Fdepraetre/PinokioProject/img/5kg_load.JPG

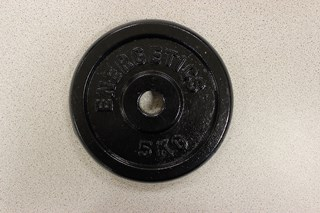
img/5kg_load.JPG
