Fdepraetre/PinokioProject/img/actuator_arm.JPG

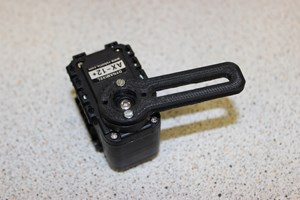
img/actuator_arm.JPG
