Fdepraetre/PinokioProject/img/arm.JPG

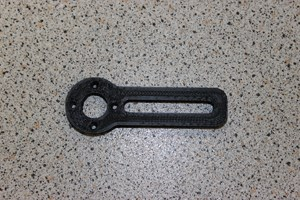
img/arm.JPG
