Fdepraetre/PinokioProject/img/baker_bowl.JPG

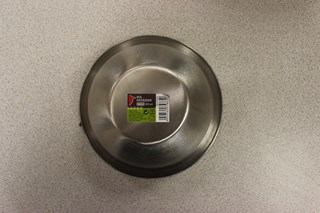
img/baker_bowl.JPG
