Fdepraetre/PinokioProject/img/base_part2_actuator_mounted_2.JPG

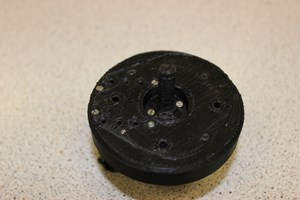
img/base_part2_actuator_mounted_2.JPG
