Fdepraetre/PinokioProject/img/common_anode_led.jpg

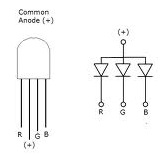
img/common_anode_led.jpg
