Fdepraetre/PinokioProject/img/finished_lamp.JPG

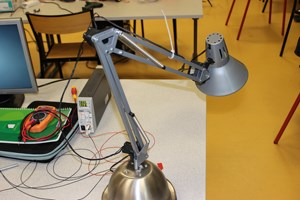
img/finished_lamp.JPG
