Fdepraetre/PinokioProject/img/finished_lamp_red.JPG

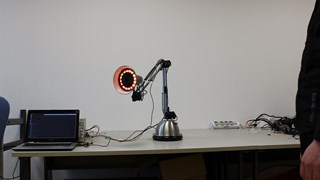
img/finished_lamp_red.JPG
