Fdepraetre/PinokioProject/img/finished_lamp_top_view.JPG

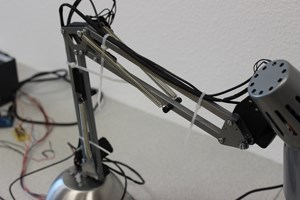
img/finished_lamp_top_view.JPG
