Fdepraetre/PinokioProject/img/head_actuator mounted.JPG

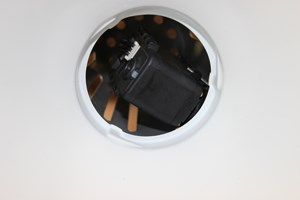
img/head_actuator mounted.JPG
