Fdepraetre/PinokioProject/img/head_actuator+joint3.JPG

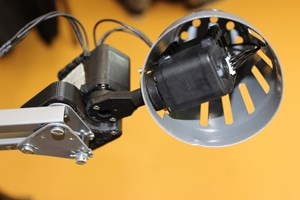
img/head_actuator+joint3.JPG
