Fdepraetre/PinokioProject/img/head_mounted2.JPG

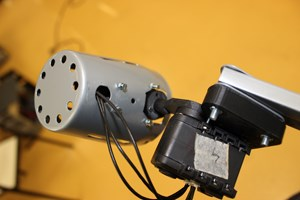
img/head_mounted2.JPG
