Fdepraetre/PinokioProject/img/joint1_mounted1.JPG

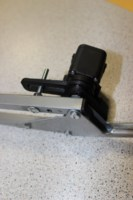
img/joint1_mounted1.JPG
