Fdepraetre/PinokioProject/img/joint1_mounted2.JPG

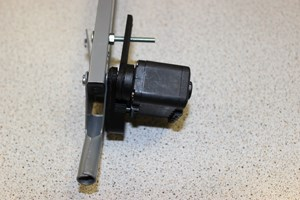
img/joint1_mounted2.JPG
