Fdepraetre/PinokioProject/img/joint1_mounted3.JPG

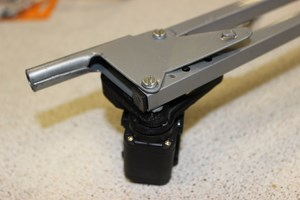
img/joint1_mounted3.JPG
