Fdepraetre/PinokioProject/img/joint1_mounted4.JPG

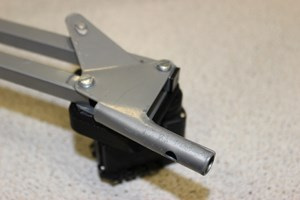
img/joint1_mounted4.JPG
