Fdepraetre/PinokioProject/img/joint2_mounted5.JPG

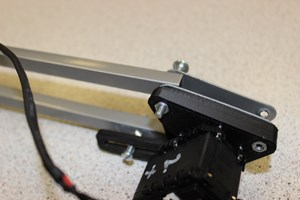
img/joint2_mounted5.JPG
