Fdepraetre/PinokioProject/img/joint2_mounted.JPG

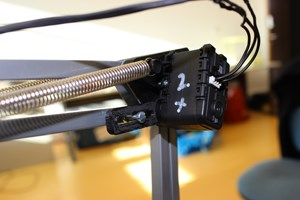
img/joint2_mounted.JPG
