Fdepraetre/PinokioProject/img/joint2_mounted_1.JPG

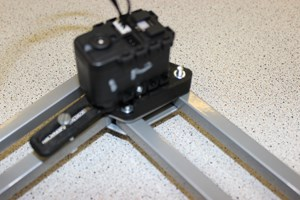
img/joint2_mounted_1.JPG
