Fdepraetre/PinokioProject/img/joint2_mounted_2.JPG

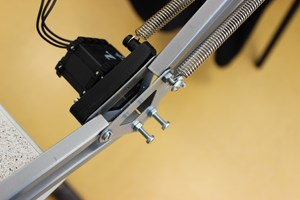
img/joint2_mounted_2.JPG
