Fdepraetre/PinokioProject/img/joint2_mounted_3.JPG

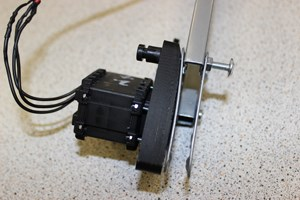
img/joint2_mounted_3.JPG
