Fdepraetre/PinokioProject/img/joint2_mounted_4.JPG

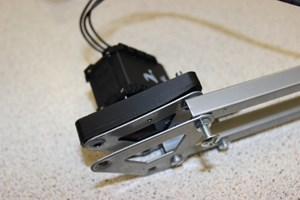
img/joint2_mounted_4.JPG
