Fdepraetre/PinokioProject/img/joint2_plastic_part.JPG

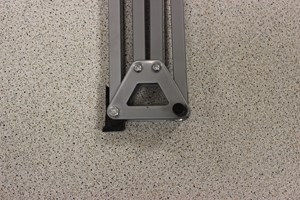
img/joint2_plastic_part.JPG
