Fdepraetre/PinokioProject/img/joint3.JPG

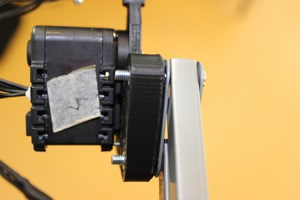
img/joint3.JPG
