Fdepraetre/PinokioProject/img/lamp_box.JPG

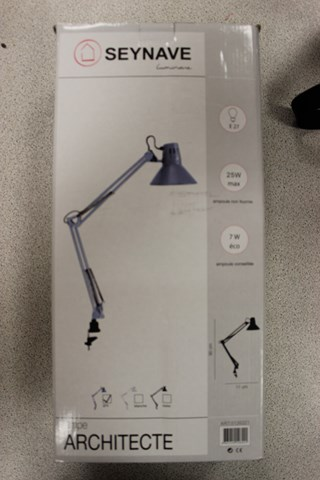
img/lamp_box.JPG
