Fdepraetre/PinokioProject/img/lamp_dissambled.JPG

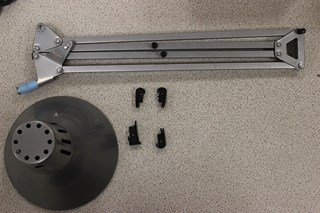
img/lamp_dissambled.JPG
