Fdepraetre/PinokioProject/img/lamp_finished_green.JPG

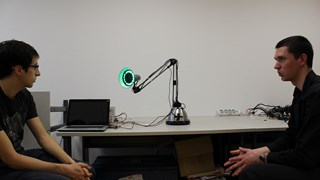
img/lamp_finished_green.JPG
