Fdepraetre/PinokioProject/img/lamp_finished_green_1.JPG

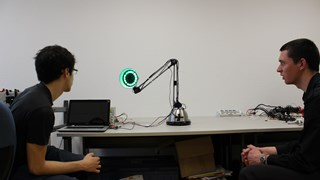
img/lamp_finished_green_1.JPG
