Fdepraetre/PinokioProject/img/lamp_led_unmounted.JPG

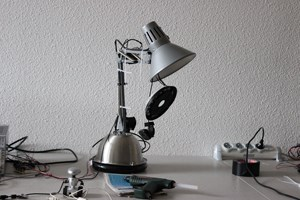
img/lamp_led_unmounted.JPG
