Fdepraetre/PinokioProject/img/lamp_top.JPG

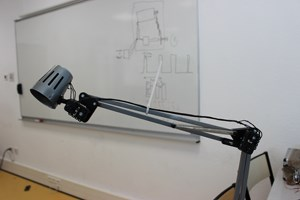
img/lamp_top.JPG
