Fdepraetre/PinokioProject/img/led_1.JPG

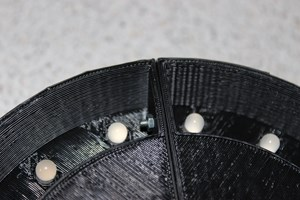
img/led_1.JPG
