Fdepraetre/PinokioProject/img/led_2.JPG

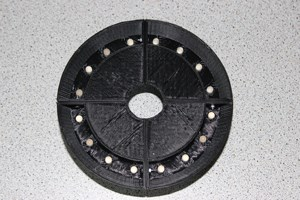
img/led_2.JPG
