Fdepraetre/PinokioProject/img/led_3.JPG

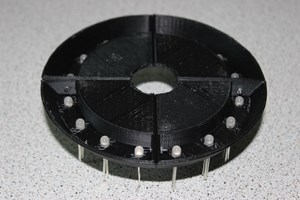
img/led_3.JPG
