Fdepraetre/PinokioProject/img/led_4.JPG

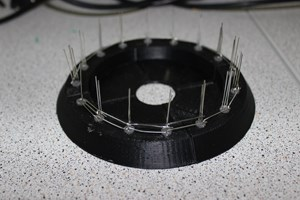
img/led_4.JPG
