Fdepraetre/PinokioProject/img/ledBoard.png

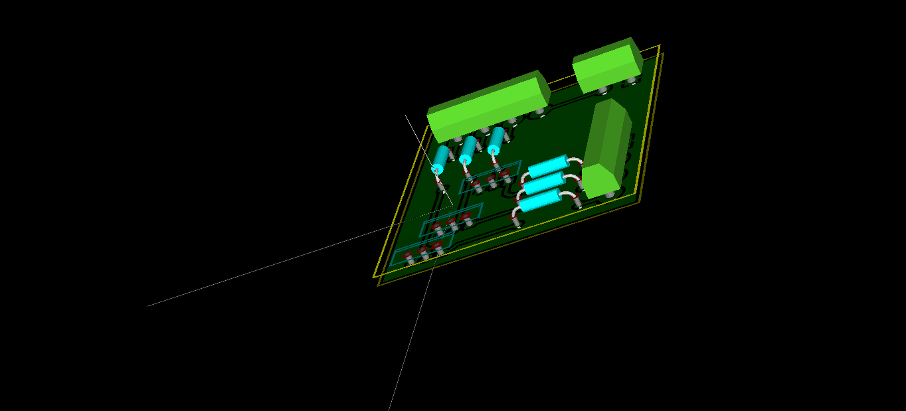
img/ledBoard.png
