Fdepraetre/PinokioProject/img/LedControlSchematic.png

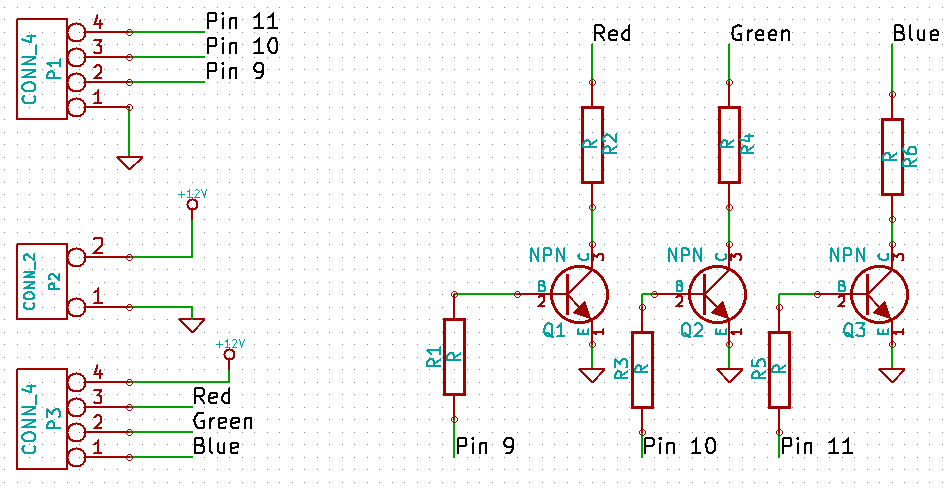
img/LedControlSchematic.png
