Fdepraetre/PinokioProject/img/part_ax12tobase.bmp

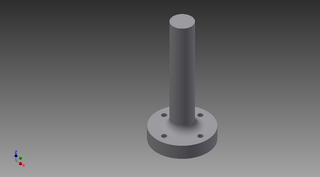
img/part_ax12tobase.bmp
