Fdepraetre/PinokioProject/img/part_bloc.bmp

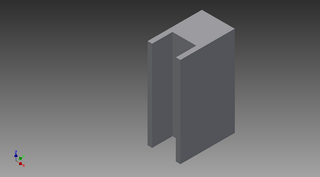
img/part_bloc.bmp
