Fdepraetre/PinokioProject/img/part_bottom_mx28_v1.bmp

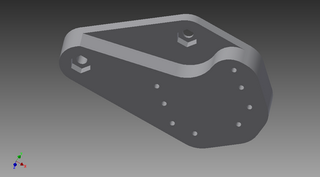
img/part_bottom_mx28_v1.bmp
