Fdepraetre/PinokioProject/img/part_bowl_ax12_support.bmp

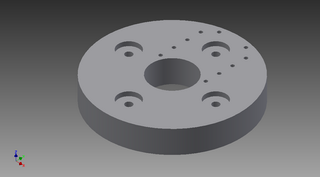
img/part_bowl_ax12_support.bmp
