Fdepraetre/PinokioProject/img/part_bowl_v1.bmp

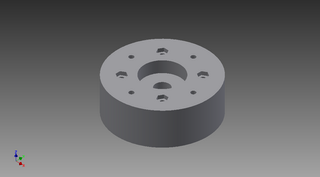
img/part_bowl_v1.bmp
