Fdepraetre/PinokioProject/img/part_head_inside.bmp

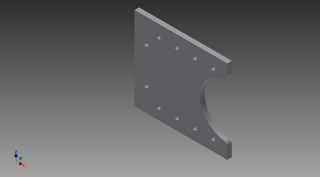
img/part_head_inside.bmp
