Fdepraetre/PinokioProject/img/part_led_circle.bmp

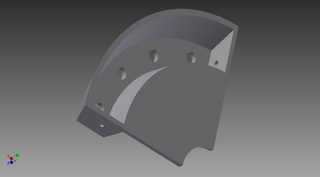
img/part_led_circle.bmp
