Fdepraetre/PinokioProject/img/part_middle_v1.bmp

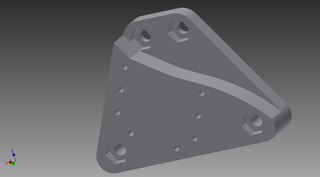
img/part_middle_v1.bmp
