Fdepraetre/PinokioProject/img/part_neck_v2.1.bmp

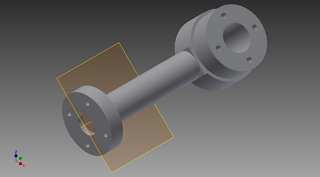
img/part_neck_v2.1.bmp
