Fdepraetre/PinokioProject/img/part_top_v4.bmp

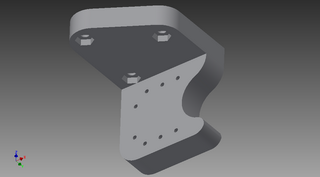
img/part_top_v4.bmp
