Fdepraetre/PinokioProject/img/square_tube_cut.JPG

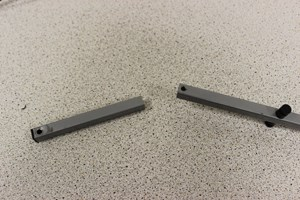
img/square_tube_cut.JPG
