Fdepraetre/PinokioProject/img/square_tube_hole.JPG

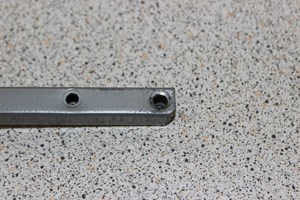
img/square_tube_hole.JPG
