Fdepraetre/PinokioProject/img/stem1.JPG

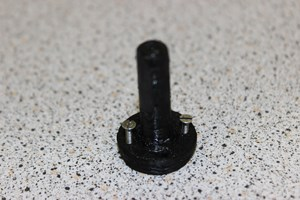
img/stem1.JPG
