Fdepraetre/PinokioProject/img/stem2.JPG

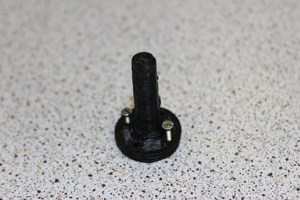
img/stem2.JPG
