Fdepraetre/PinokioProject/img/tube_drilled1.JPG

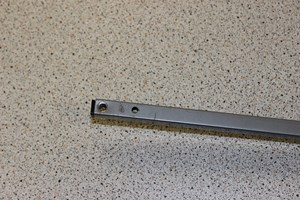
img/tube_drilled1.JPG
