Fdepraetre/PinokioProject/img/tube_drilled2.JPG

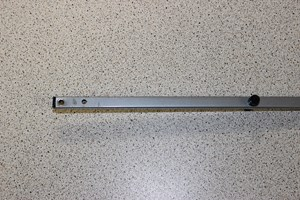
img/tube_drilled2.JPG
