Fdepraetre/PinokioProject/img/usb2dynamixel.JPG

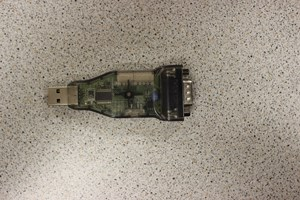
img/usb2dynamixel.JPG
