Fdepraetre/PinokioProject/parts/head_inside.stl

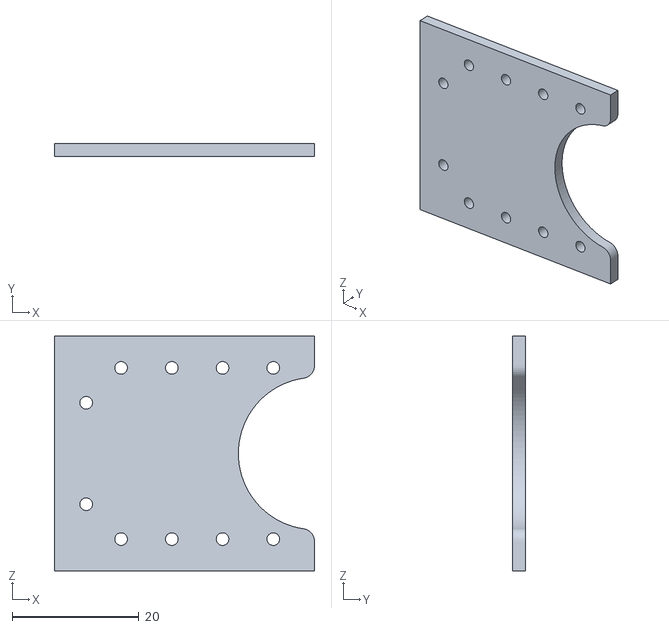
[picture p73: CAD file, 2014-01-16]
parts/head_inside.stl
41.0 x 2.00 x 37.0
