Fdepraetre/PinokioProject/parts/middle_v1.stl

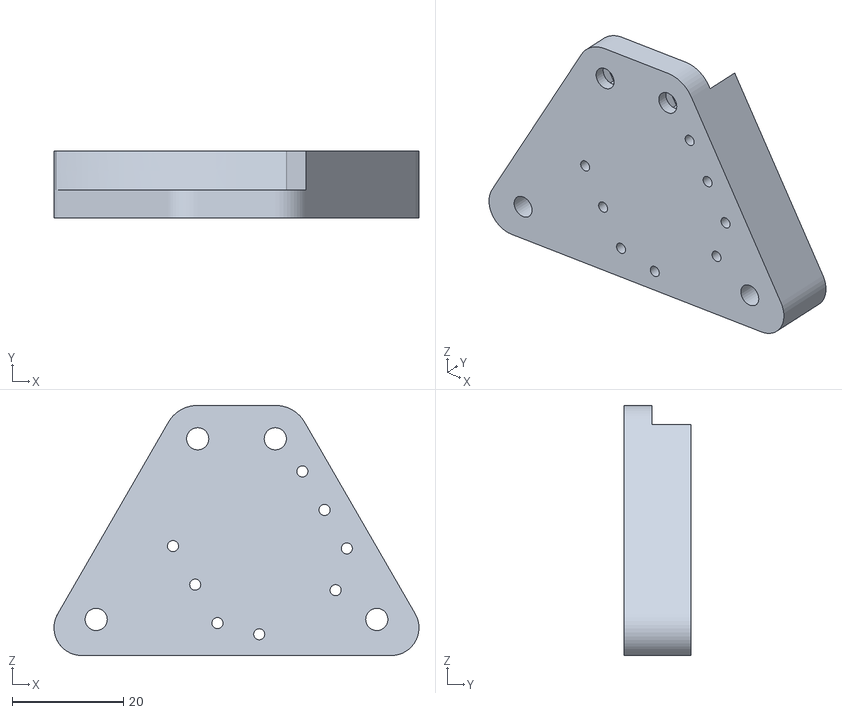
[picture p74: CAD file, 2014-01-14]
parts/middle_v1.stl
65.7 x 12.0 x 45.0
