Fdepraetre/PinokioProject/parts/oldparts/bowl_v1.stl

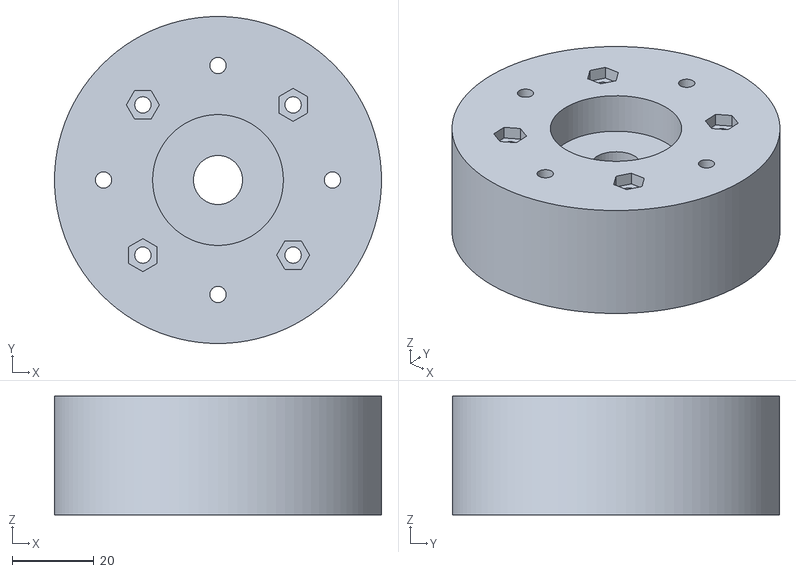
[picture p75: CAD file, 2014-01-16]
parts/oldparts/bowl_v1.stl
80.0 x 80.0 x 29.0
