Fdepraetre/PinokioProject/parts/top_circle.stl

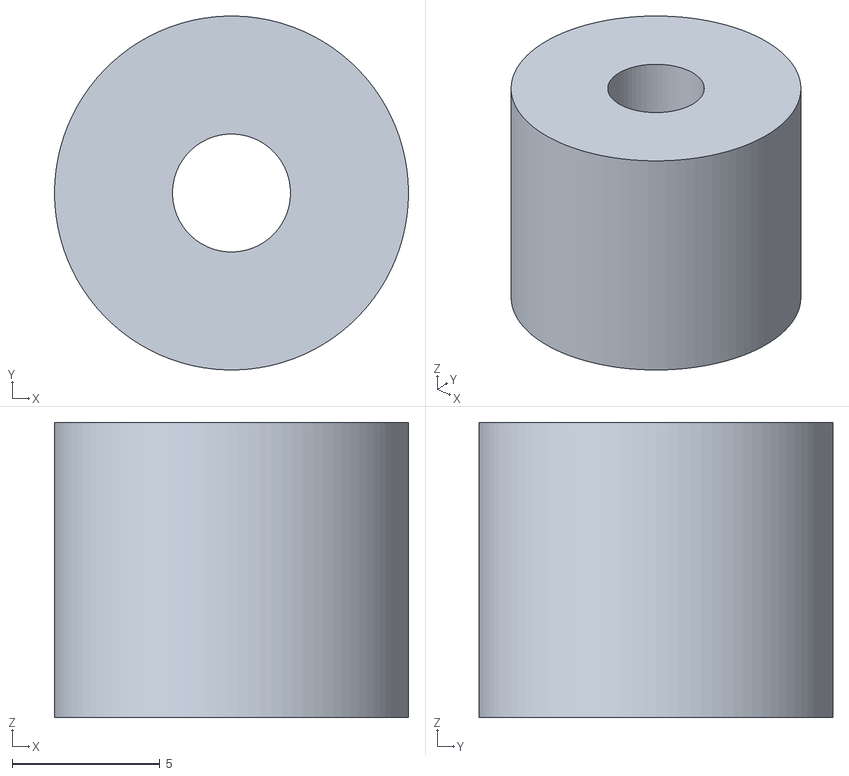
[picture p76: CAD file, 2014-01-14]
parts/top_circle.stl
12.0 x 12.0 x 10.0
