Fdepraetre/PinokioProject/parts/moving_arm.stl

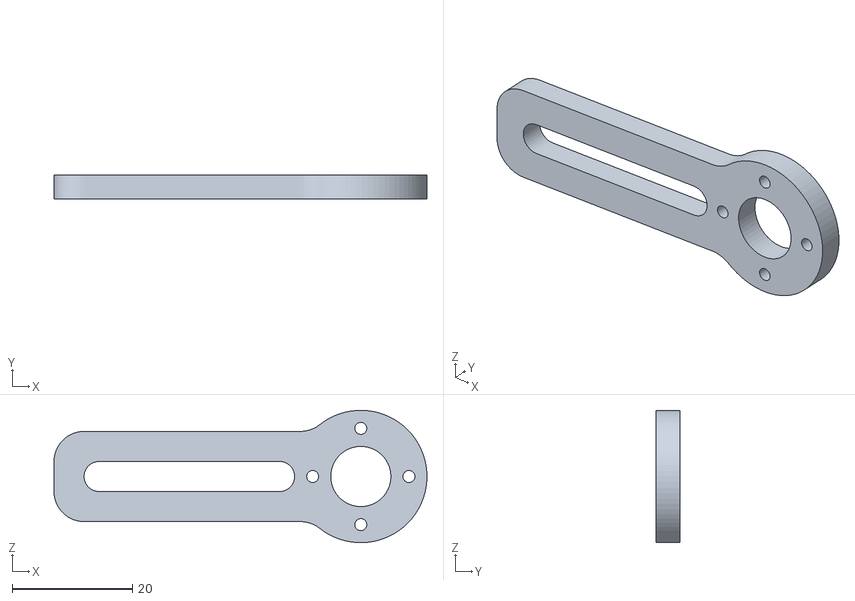
[picture p77: CAD file, 2014-01-14]
parts/moving_arm.stl
62.0 x 4.00 x 22.0
