Fdepraetre/PinokioProject/img/base_step2.JPG

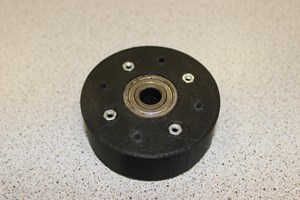
img/base_step2.JPG
