Fdepraetre/PinokioProject/img/base_step3.JPG

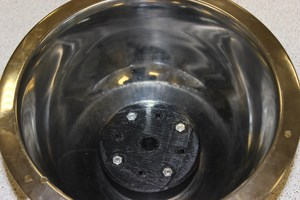
img/base_step3.JPG
