Fdepraetre/PinokioProject/img/base_step4.JPG

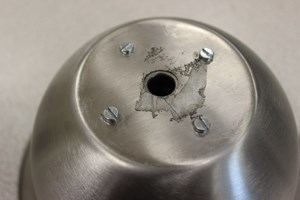
img/base_step4.JPG
