Fdepraetre/PinokioProject/img/base_step5.JPG

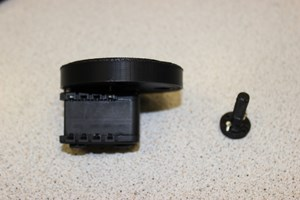
img/base_step5.JPG
