Fdepraetre/PinokioProject/img/base_step7.JPG

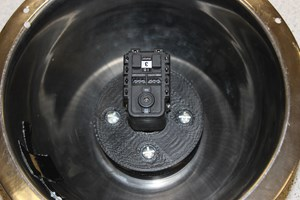
img/base_step7.JPG
