Fdepraetre/PinokioProject/img/base_step8.JPG

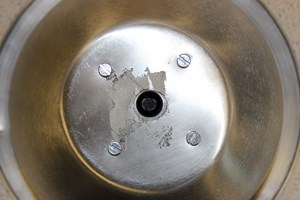
img/base_step8.JPG
