Fdepraetre/PinokioProject/img/bowl_step3.JPG

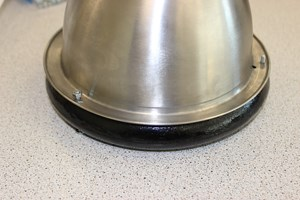
img/bowl_step3.JPG
