Fdepraetre/PinokioProject/img/bowl_step4.JPG

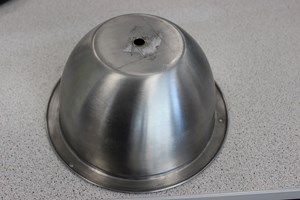
img/bowl_step4.JPG
