Fdepraetre/PinokioProject/img/bowl_step5.JPG

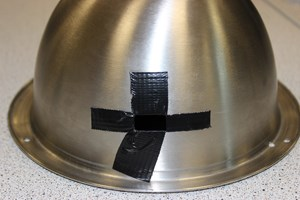
img/bowl_step5.JPG
