Fdepraetre/PinokioProject/img/head_step1-2.JPG

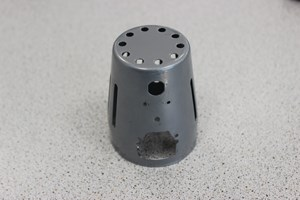
img/head_step1-2.JPG
