Fdepraetre/PinokioProject/img/head_step1.JPG

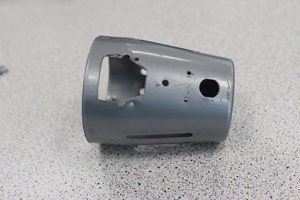
img/head_step1.JPG
