Fdepraetre/PinokioProject/img/head_step2-2.JPG

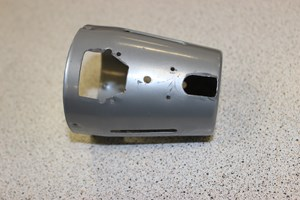
img/head_step2-2.JPG
