Fdepraetre/PinokioProject/img/head_step2.JPG

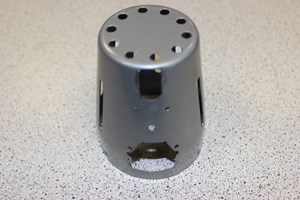
img/head_step2.JPG
