Fdepraetre/PinokioProject/img/head_step3-2.JPG

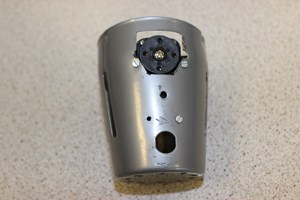
img/head_step3-2.JPG
