Fdepraetre/PinokioProject/img/head_step3.JPG

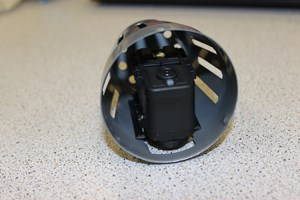
img/head_step3.JPG
