Fdepraetre/PinokioProject/img/head_step4.JPG

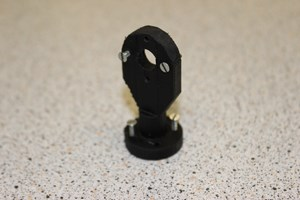
img/head_step4.JPG
