Fdepraetre/PinokioProject/img/head_step5.JPG

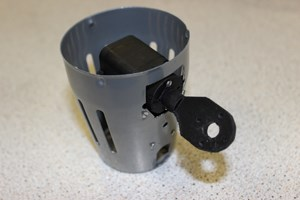
img/head_step5.JPG
