Fdepraetre/PinokioProject/img/joint1_step0.JPG

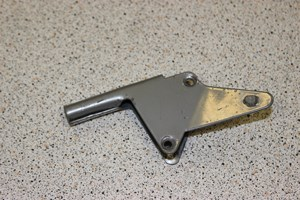
img/joint1_step0.JPG
