Fdepraetre/PinokioProject/img/joint1_step1.JPG

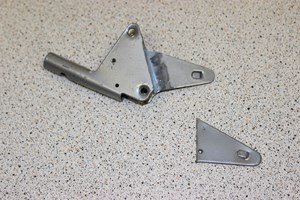
img/joint1_step1.JPG
