Fdepraetre/PinokioProject/img/joint1_step2.JPG

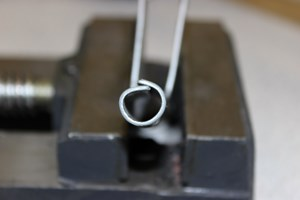
img/joint1_step2.JPG
