Fdepraetre/PinokioProject/img/joint1_step3.JPG

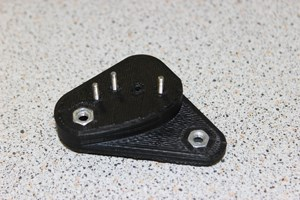
img/joint1_step3.JPG
