Fdepraetre/PinokioProject/img/joint2_step1.JPG

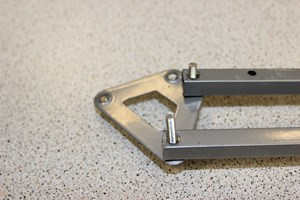
img/joint2_step1.JPG
