Fdepraetre/PinokioProject/img/joint2_step2.JPG

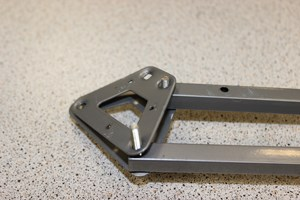
img/joint2_step2.JPG
