Fdepraetre/PinokioProject/img/joint2_step3.JPG

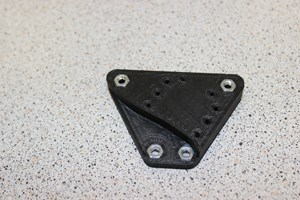
img/joint2_step3.JPG
