Fdepraetre/PinokioProject/img/joint2_step4.JPG

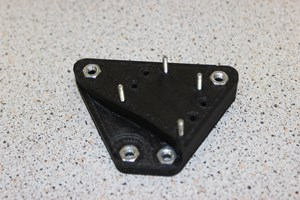
img/joint2_step4.JPG
