Fdepraetre/PinokioProject/img/joint2_step5.JPG

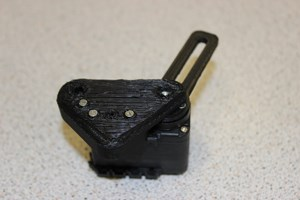
img/joint2_step5.JPG
