Fdepraetre/PinokioProject/img/joint2_step6.JPG

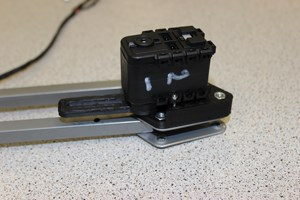
img/joint2_step6.JPG
