Fdepraetre/PinokioProject/img/joint2_step8.JPG

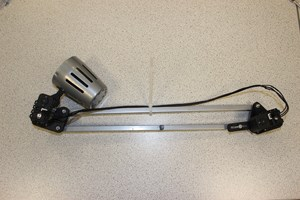
img/joint2_step8.JPG
