Fdepraetre/PinokioProject/img/joint3_step1.JPG

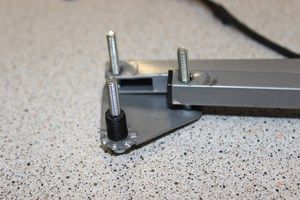
img/joint3_step1.JPG
