Fdepraetre/PinokioProject/img/joint3_step2.JPG

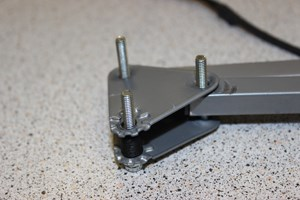
img/joint3_step2.JPG
