Fdepraetre/PinokioProject/img/joint3_step3.JPG

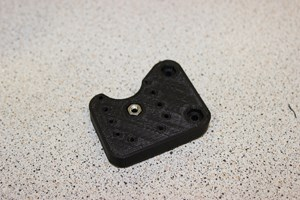
img/joint3_step3.JPG
