Fdepraetre/PinokioProject/img/joint3_step4.JPG

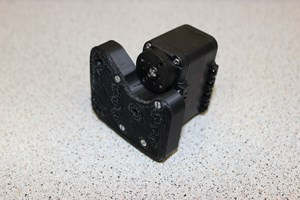
img/joint3_step4.JPG
