Fdepraetre/PinokioProject/img/joint3_step5-2.JPG

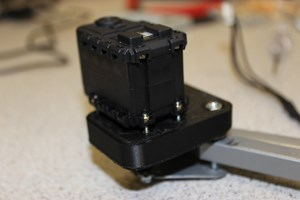
img/joint3_step5-2.JPG
