Fdepraetre/PinokioProject/img/joint3_step5.JPG

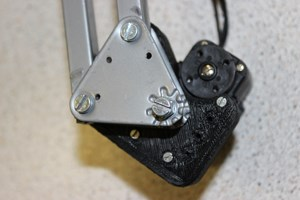
img/joint3_step5.JPG
