Fdepraetre/PinokioProject/img/joint3_step6.JPG

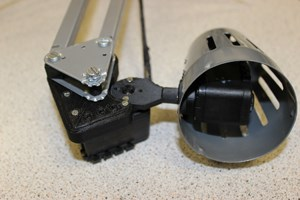
img/joint3_step6.JPG
