Fdepraetre/PinokioProject/img/led_step0.JPG

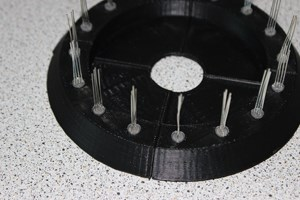
img/led_step0.JPG
