Fdepraetre/PinokioProject/img/led_step1.JPG

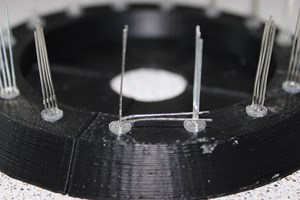
img/led_step1.JPG
