Fdepraetre/PinokioProject/img/led_step3.JPG

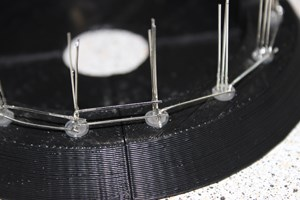
img/led_step3.JPG
