Fdepraetre/PinokioProject/img/led_step4.JPG

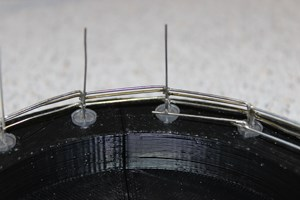
img/led_step4.JPG
