Fdepraetre/PinokioProject/img/led_step5.JPG

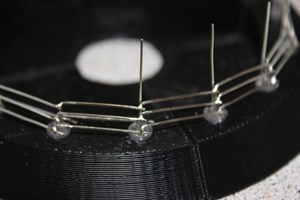
img/led_step5.JPG
