Fdepraetre/PinokioProject/img/led_step6.JPG

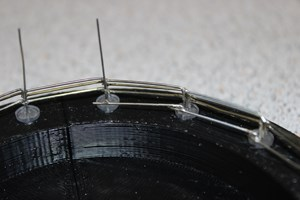
img/led_step6.JPG
