Fdepraetre/PinokioProject/img/led_step7.JPG

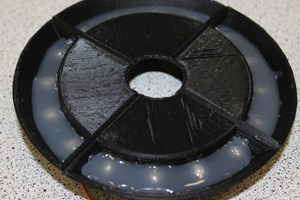
img/led_step7.JPG
