Fdepraetre/PinokioProject/img/led_step8.JPG

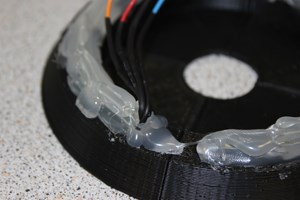
img/led_step8.JPG
