Fdepraetre/PinokioProject/img/led_step9.JPG

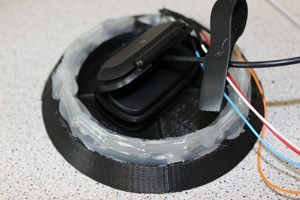
img/led_step9.JPG
