Fdepraetre/PinokioProject/img/led_step10.JPG

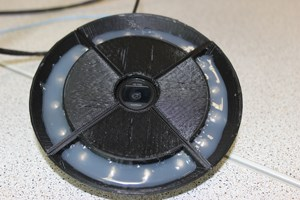
img/led_step10.JPG
