Fdepraetre/PinokioProject/img/load_step1.JPG

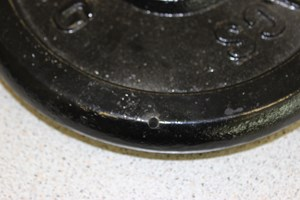
img/load_step1.JPG
