Fdepraetre/PinokioProject/img/load_step2.JPG

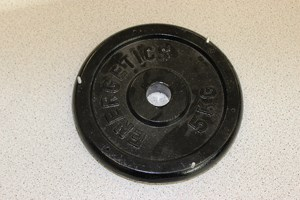
img/load_step2.JPG
