Fdepraetre/PinokioProject/elec/led.sch

## KiCad design elec/led.sch (2014-01-29)

Schematic: led.sch

Parts:
P1, P3: CONN_4
P2: CONN_2
Q1, Q2, Q3: NPN
R1, R2, R3, R4, R5, R6: R
