Fdepraetre/PinokioProject/src/userInterface/gui.py

import sys
import wx
import time
import threading
sys.path.insert(0, "../settings/")
import settings
sys.path.insert(0, "../control/")
import motorControl
sys.path.insert(0, "../traj/")
import trajectoryController
sys.path.insert(0, "../arduino/")
import python2arduino

class MyFrame(wx.Frame):
    def __init__(self, parent, id, title):
        wx.Frame.__init__(self, parent, id, title, wx.DefaultPosition, (800, 600))

        hbox= wx.BoxSizer(wx.HORIZONTAL)
        vbox = wx.BoxSizer(wx.VERTICAL)
        hboxcontrols = wx.BoxSizer(wx.HORIZONTAL)
        hboxlist = wx.BoxSizer(wx.HORIZONTAL)

        vbox.Add(hboxcontrols, 1, wx.EXPAND)
        vbox.Add(hboxlist, 1, wx.EXPAND)

        #comment load motor and load led when working on gui
        #load motor
        motorSettings = settings.MotorSettings().get()
        self.motorController = motorControl.MotorControl(motorSettings)
        self.motorController.setAllSpeed(100)
        #parse motor setting to get min and max angle, store result in hash motors
        motors = {}
        motorsConfig=motorSettings["motorConfig"]
        for motor in motorsConfig:
            motors[motor[3]] = [motor[1], motor[2]]

        #load led
        self.ledController = python2arduino.Arduino()

        #uncomment when working on gui
        #motors = {"bowl": [0, 150], "bottom": [0, 150], "mid": [0, 150], "top": [0, 150], "head": [0, 150]}

        #visual element
  
        #bowl button
        pnlBowl = wx.Panel(self, -1, style=wx.SIMPLE_BORDER)
        hboxcontrols.Add(pnlBowl, 1, wx.ALL |wx.EXPAND, 1)
        self.sldBowl = wx.Slider(pnlBowl, -1, motors["bowl"][0], motors["bowl"][0], motors["bowl"][1], wx.DefaultPosition, (-1, -1), wx.SL_VERTICAL | wx.SL_LABELS)
        textBowl = wx.StaticText(pnlBowl, -1, 'Bowl')
        vboxBowl = wx.BoxSizer(wx.VERTICAL)
        vboxBowl.Add(self.sldBowl, 1, wx.CENTER, 0)
        vboxBowl.Add(textBowl, 1, wx.CENTER)
        pnlBowl.SetSizer(vboxBowl)

        #bottom button
        pnlBottom = wx.Panel(self, -1, style=wx.SIMPLE_BORDER)
        hboxcontrols.Add(pnlBottom, 1, wx.ALL | wx.EXPAND, 1)
        self.sldBottom = wx.Slider(pnlBottom, -1, motors["bottom"][1], motors["bottom"][0], motors["bottom"][1], wx.DefaultPosition, (-1, -1), wx.SL_VERTICAL | wx.SL_LABELS)
        textBottom = wx.StaticText(pnlBottom, -1, 'Bottom')
        vboxBottom = wx.BoxSizer(wx.VERTICAL)
        vboxBottom.Add(self.sldBottom, 1, wx.CENTER)
        vboxBottom.Add(textBottom, 1, wx.CENTER)
        pnlBottom.SetSizer(vboxBottom)

        #middle button
        pnlMiddle = wx.Panel(self, -1, style=wx.SIMPLE_BORDER)
        hboxcontrols.Add(pnlMiddle, 1, wx.ALL | wx.EXPAND, 1)
        self.sldMiddle = wx.Slider(pnlMiddle, -1, motors["mid"][0], motors["mid"][0], motors["mid"][1], wx.DefaultPosition, (-1, -1), wx.SL_VERTICAL | wx.SL_LABELS)
        textMiddle = wx.StaticText(pnlMiddle, -1, 'Middle')
        vboxMiddle= wx.BoxSizer(wx.VERTICAL)
        vboxMiddle.Add(self.sldMiddle, 1, wx.CENTER)
        vboxMiddle.Add(textMiddle, 1, wx.CENTER)
        pnlMiddle.SetSizer(vboxMiddle)

        #top button
        pnlTop = wx.Panel(self, -1, style=wx.SIMPLE_BORDER)
        hboxcontrols.Add(pnlTop, 1, wx.ALL | wx.EXPAND, 1)
        self.sldTop = wx.Slider(pnlTop, -1, motors["top"][0], motors["top"][0], motors["top"][1], wx.DefaultPosition, (-1, -1), wx.SL_VERTICAL | wx.SL_LABELS)
        textTop = wx.StaticText(pnlTop, -1, 'Top')
        vboxTop = wx.BoxSizer(wx.VERTICAL)
        vboxTop.Add(self.sldTop, 1, wx.CENTER)
        vboxTop.Add(textTop, 1, wx.CENTER)
        pnlTop.SetSizer(vboxTop)

        #head button
        pnlHead = wx.Panel(self, -1, style=wx.SIMPLE_BORDER)
        hboxcontrols.Add(pnlHead, 1, wx.ALL | wx.EXPAND, 1)
        self.sldHead = wx.Slider(pnlHead, -1, motors["head"][0], motors["head"][0], motors["head"][1], wx.DefaultPosition, (-1, -1), wx.SL_VERTICAL | wx.SL_LABELS)
        textHead = wx.StaticText(pnlHead, -1, 'Head')
        vboxHead = wx.BoxSizer(wx.VERTICAL)
        vboxHead.Add(self.sldHead, 1, wx.CENTER)
        vboxHead.Add(textHead, 1, wx.CENTER)
        pnlHead.SetSizer(vboxHead)

        #red button
        pnlRed = wx.Panel(self, -1, style=wx.SIMPLE_BORDER)
        hboxcontrols.Add(pnlRed, 1, wx.ALL | wx.EXPAND, 1)
        self.sldRed = wx.Slider(pnlRed, -1, 0, 0, 255, wx.DefaultPosition, (-1, -1), wx.SL_VERTICAL | wx.SL_LABELS)
        textRed = wx.StaticText(pnlRed, -1, 'Red')
        vboxRed = wx.BoxSizer(wx.VERTICAL)
        vboxRed.Add(self.sldRed, 1, wx.CENTER)
        vboxRed.Add(textRed, 1, wx.CENTER)
        pnlRed.SetSizer(vboxRed)

        #green button
        pnlGreen = wx.Panel(self, -1, style=wx.SIMPLE_BORDER)
        hboxcontrols.Add(pnlGreen, 1, wx.ALL | wx.EXPAND, 1)
        self.sldGreen = wx.Slider(pnlGreen, -1, 0, 0, 255, wx.DefaultPosition, (-1, -1), wx.SL_VERTICAL | wx.SL_LABELS)
        textGreen = wx.StaticText(pnlGreen, -1, 'Green')
        vboxGreen = wx.BoxSizer(wx.VERTICAL)
        vboxGreen.Add(self.sldGreen, 1, wx.CENTER)
        vboxGreen.Add(textGreen, 1, wx.CENTER)
        pnlGreen.SetSizer(vboxGreen)

        #blue button
        pnlBlue = wx.Panel(self, -1, style=wx.SIMPLE_BORDER)
        hboxcontrols.Add(pnlBlue, 1, wx.ALL | wx.EXPAND, 1)
        self.sldBlue = wx.Slider(pnlBlue, -1, 0, 0, 255, wx.DefaultPosition, (-1, -1), wx.SL_VERTICAL | wx.SL_LABELS)
        textBlue = wx.StaticText(pnlBlue, -1, 'Blue')
        vboxBlue = wx.BoxSizer(wx.VERTICAL)
        vboxBlue.Add(self.sldBlue, 1, wx.CENTER)
        vboxBlue.Add(textBlue, 1, wx.CENTER)
        pnlBlue.SetSizer(vboxBlue)


        #buttons
        pnlButtons = wx.Panel(self, -1, style=wx.SIMPLE_BORDER)
        vboxButton = wx.BoxSizer(wx.VERTICAL)
        
        gotoButton = wx.Button(pnlButtons, 7, 'Go To')
        vboxButton.Add(gotoButton, 1, wx.ALIGN_CENTER | wx.TOP, 15)
        wx.EVT_BUTTON(self, 7, self.OnGoto)

        savePositionButton = wx.Button(pnlButtons, 8, 'Save to list')
        vboxButton.Add(savePositionButton, 1, wx.ALIGN_CENTER | wx.TOP, 15)
        wx.EVT_BUTTON(self, 8, self.OnSavePosition)

        deletePositionButton = wx.Button(pnlButtons, 9, 'Delete from list')
        vboxButton.Add(deletePositionButton, 1, wx.ALIGN_CENTER | wx.TOP, 15)
        wx.EVT_BUTTON(self, 9, self.OnDeletePosition)

        playButton = wx.Button(pnlButtons, 10, 'Play')
        vboxButton.Add(playButton, 1, wx.ALIGN_CENTER | wx.TOP, 15)
        wx.EVT_BUTTON(self, 10, self.OnPlay)
        
        stopButton = wx.Button(pnlButtons, 11, 'Stop')
        vboxButton.Add(stopButton, 1, wx.ALIGN_CENTER | wx.TOP | wx.BOTTOM, 15)
        wx.EVT_BUTTON(self, 11, self.OnStop)
        
        pnlButtons.SetSizer(vboxButton)
        
        #list of position
        self.positionList = wx.ListCtrl(self, -1, style=wx.LC_REPORT)
        self.positionList.InsertColumn(0, 'bowl')
        self.positionList.InsertColumn(1, 'bottom')
        self.positionList.InsertColumn(2, 'middle')
        self.positionList.InsertColumn(3, 'top')
        self.positionList.InsertColumn(4, 'head')
        self.positionList.InsertColumn(5, 'red')
        self.positionList.InsertColumn(6, 'green')
        self.positionList.InsertColumn(7, 'blue')
        hboxlist.Add(self.positionList, 1, wx.EXPAND)

        hbox.Add(vbox, 5, wx.EXPAND | wx.ALL, 1)
        hbox.Add(pnlButtons, 1, wx.EXPAND | wx.ALL, 1)
        self.SetSize((800, 600))
        self.SetSizer(hbox)
        self.Centre()


    def OnPlay(self, event):
        count = self.positionList.GetItemCount()
        listMove = []
        listLed = []
        for row in range(count):
            tmpListMove = []
            value = int(self.positionList.GetItem(row, 0).GetText())
            tmpListMove.append(["bowl", value])
            value = int(self.positionList.GetItem(row, 1).GetText())
            tmpListMove.append(["bottom", value])
            value = int(self.positionList.GetItem(row, 2).GetText())
            tmpListMove.append(["mid", value])
            value = int(self.positionList.GetItem(row, 3).GetText())
            tmpListMove.append(["top", value])
            value = int(self.positionList.GetItem(row, 4).GetText())
            tmpListMove.append(["head", value])
            listMove.append(tmpListMove)

            tmpListLed = []
            value = int(self.positionList.GetItem(row, 5).GetText())
            tmpListLed.append(value)
            value = int(self.positionList.GetItem(row, 6).GetText())
            tmpListLed.append(value)
            value = int(self.positionList.GetItem(row, 7).GetText())
            tmpListLed.append(value)
            listLed.append(tmpListLed)

        #thread for sequence of movement
        self.play = PlayMove(self.motorController, self.ledController)
        self.play.listMove(listMove)
        self.play.listLed(listLed)
        self.play.start()

    def OnStop(self, event):
        #print "caramel"
        self.play.stop()

    def OnGoto(self, event):

        red = self.sldRed.GetValue()
        green = self.sldGreen.GetValue()
        blue = self.sldBlue.GetValue()
        self.ledController.lightLed(red, green, blue)

        listMove = []
        listMove.append(["bowl", self.sldBowl.GetValue()])
        listMove.append(["bottom", self.sldBottom.GetValue()])
        listMove.append(["mid", self.sldMiddle.GetValue()])
        listMove.append(["top", self.sldTop.GetValue()])
        listMove.append(["head", self.sldHead.GetValue()])
        self.motorController.setAllSpeed(100)
        self.motorController.setMotorsByName(listMove)

    def OnSavePosition(self, event):
        num_positions = self.positionList.GetItemCount()
        self.positionList.InsertStringItem(num_positions, str(self.sldBowl.GetValue()))
        self.positionList.SetStringItem(num_positions, 1, str(self.sldBottom.GetValue()))
        self.positionList.SetStringItem(num_positions, 2, str(self.sldMiddle.GetValue()))
        self.positionList.SetStringItem(num_positions, 3, str(self.sldTop.GetValue()))
        self.positionList.SetStringItem(num_positions, 4, str(self.sldHead.GetValue()))
        self.positionList.SetStringItem(num_positions, 5, str(self.sldRed.GetValue()))
        self.positionList.SetStringItem(num_positions, 6, str(self.sldGreen.GetValue()))
        self.positionList.SetStringItem(num_positions, 7, str(self.sldBlue.GetValue()))

    def OnDeletePosition(self, event):
        while self.positionList.GetSelectedItemCount() != 0 :
            index = self.positionList.GetFirstSelected()
            self.positionList.DeleteItem(index)

class MyApp(wx.App):
    def OnInit(self):
        frame = MyFrame(None, -1, 'Pinokio alpha 0.1')
        frame.Show(True)
        frame.Centre()
        return True

def getValueList(l):
  res = []
  for move in l:
    res.append(move[1])
  return res

#this class handle moves sequence, in a thread. So that GUI is not block when moves sequence is launched
class PlayMove(threading.Thread):
    def __init__(self, motorController, ledController):
        threading.Thread.__init__(self)
        #init stop flog to false
        self.play = False
        self.stoplock = threading.Lock()

        #initialize motor and led controller
        self.motorController = motorController
        self.ledController = ledController

    def run(self):
        #set the stop flag to true
        self.play = True
        index = 0

        #Go to initial position
        #print self.moves[0]
        self.motorController.setMotorsByName(self.moves[0])

        #set led color to initial color
        currentLedColor=self.led[0]
        self.ledController.lightLed(int(currentLedColor[0]), int(currentLedColor[1]), int(currentLedColor[2]))

        #wait for the end of the move
        time.sleep(3)
        
        if len(self.moves) > 1 :
          traj = trajectoryController.TrajectoryController(100,40,len(self.moves[0]))
          traj.set(getValueList(self.moves[0]),getValueList(self.moves[1]))
          #while stop button have not been pressed
          while self.play :
            #if motors haven't reach the position
            if not traj.update():
              self.motorController.setAllSpeed(int(traj.speed))
              values = [["bowl",traj.position[0]],
                        ["bottom",traj.position[1]],
                        ["mid",traj.position[2]],
                        ["top",traj.position[3]],
                        ["head",traj.position[4]]]
              self.motorController.setMotorsByName(values)
            #if motors are in final position
            else :
                #increment index but keep it in list length
                index = (index + 1) % len(self.moves)
                #set a new trajectory between the current position and the next position
                traj.set(getValueList(self.moves[index]), getValueList(self.moves[(index + 1) % len(self.moves)]))
                #change led color
                currentLedColor = self.led[index]
                self.ledController.lightLed(currentLedColor[0], currentLedColor[1], currentLedColor[2])

              

    def stop(self):
        with self.stoplock:
            #set stop flag to false
            #moves sequence's stop and the thread can be deleted
            self.play = False

    def listMove(self, list):
        with self.stoplock:
            #update list of moves
            self.moves = list

    def listLed(self, list):
        with self.stoplock:
            #update list of colors
            self.led = list
